chriskp-pdx/COATL-RADAR/Assignments/Exercises/ECE 413 3 Minute Exercises (4_4_2025).docx

Part 1. Constraints and Risks

1. Time. Money, but we don’t need much. Basically have everything we already need.
2. Not much. Testing is slow, but we’re chugging along. We also do have only one prototype currently that is being used for testing, but we are working on making more prototypes.
3. Successfully getting our machine learning program to work. Consistency of amplitude across tests. Testing in general is time-consuming.

Part 2. Mitigations

1. We found our stride already and are on target to complete our “must” requirements.
2. Yes, if we get more prototypes we can work in parallel on testing moving forward.
3. See 2.
