chriskp-pdx/COATL-RADAR/Software/Data Collection/Datasets/Roasted Bean Comparison.docx

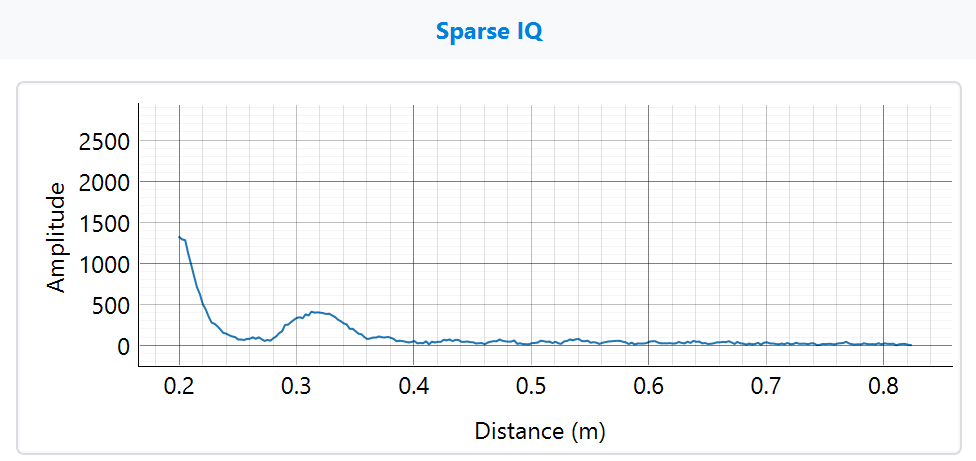
[picture p23: figure]

Dark Roast

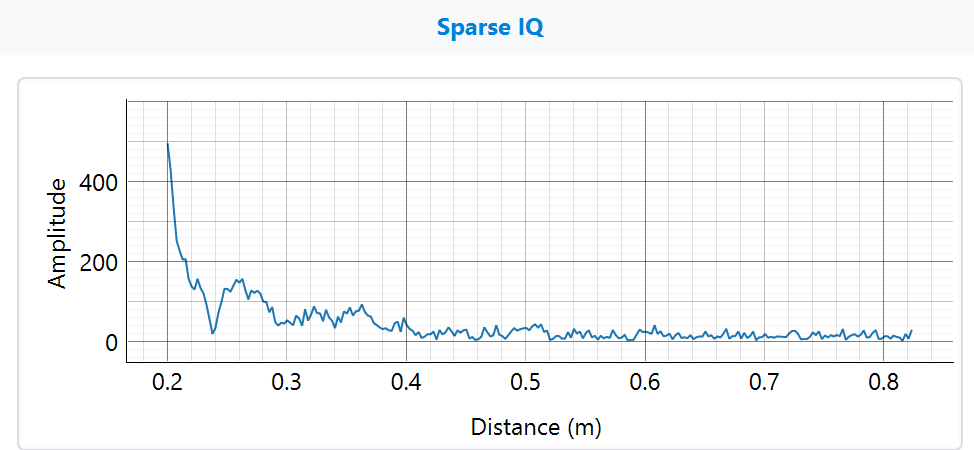
[picture p24: figure]

Medium Roast

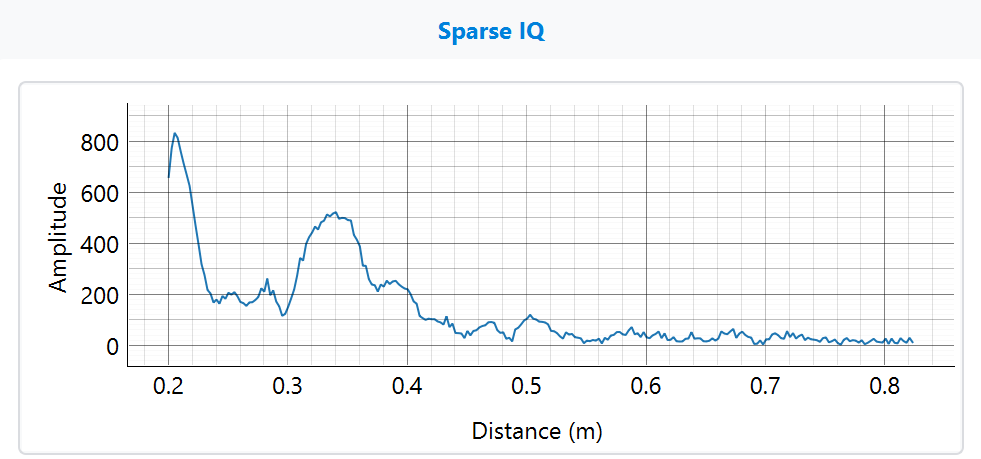
[picture p25: figure]

Light Roast
