chriskp-pdx/COATL-RADAR/Documentation/Test Documentation/Metal Device Testing/1-10 Bean Range Tests/Lens 2 Testing/README.docx

Beanis testing process Lens 2

Each bean type will have the exact same process for each

1. Start with no beans in the Beanis. Take a screenshot.
2. Add one bean. And repeat the process
3. Continue up until desired beans are in the beanis, repeat with other flavors and or lens combinations.
4. Because the beanis was not specifically made for this lens, I will be running through this test twice to simulate different orientations

After each flavor, I stopped and restarted the IQ just to start fresh

The recorded picture for each amount of beans will be found in this drive and sorted by the bean type. This will be a living drive that I will add more bean types to.

The naming convention for photos will be as follows

NameOfCoffee_NumberOfBeans_Before/AfterShaking

Kamal Notes:

Weird change in amplitude around 7 or 8 beans, will need to test this amount more
