chriskp-pdx/COATL-RADAR/Documentation/Test Documentation/Metal Device Testing/1-10 Bean Range Tests/Lens 1 Testing/Bean Testing Part 1.pptx

## Bean Testing

1. Start with no beans in the Beanis. Take a screenshot.
2. To keep consistent, I will be picking up and inverting the Bean-tube to simulate moving the beans around even without any beans in there. Take another screenshot after movement so you have a before shaking and after shaking picture.
3. Add one bean. And repeat the process
4. Continue up until desired beans are in the bean-tube, repeat with other flavors and or lens combinations. (I will be focusing on the lens the bean-tube was modeled for)

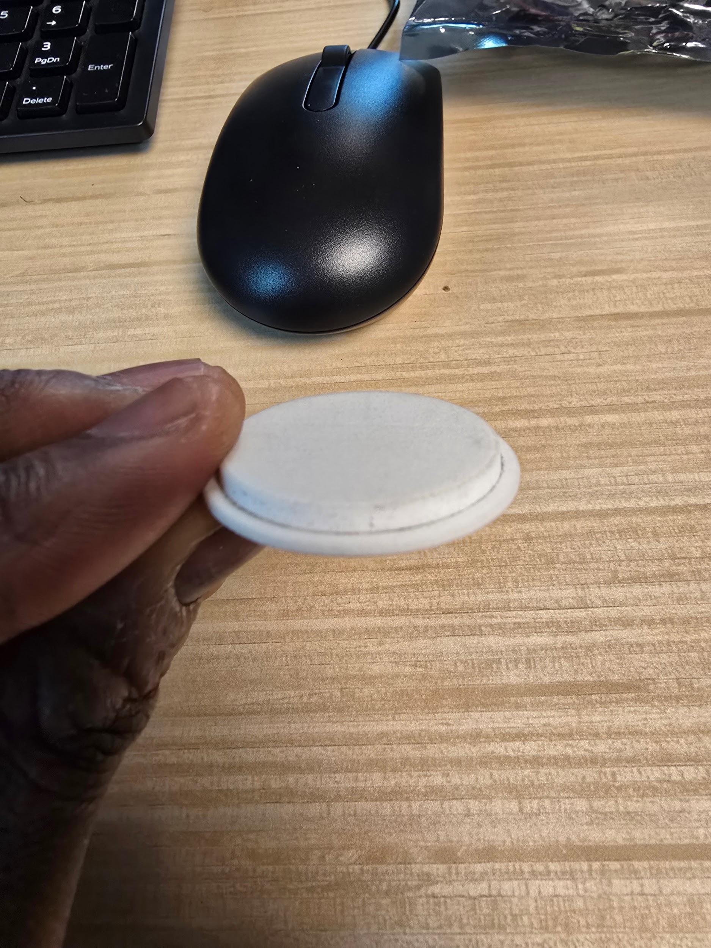
[picture p122: figure]

## Settings

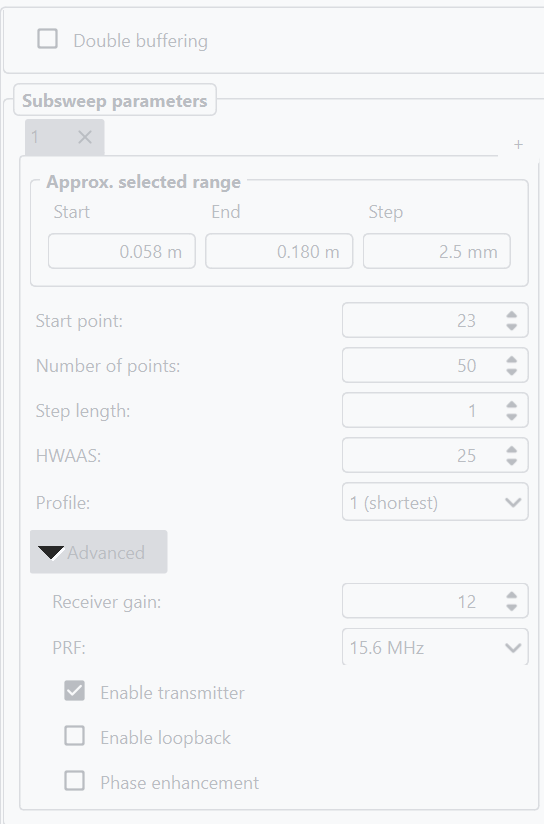
[picture p123: figure]
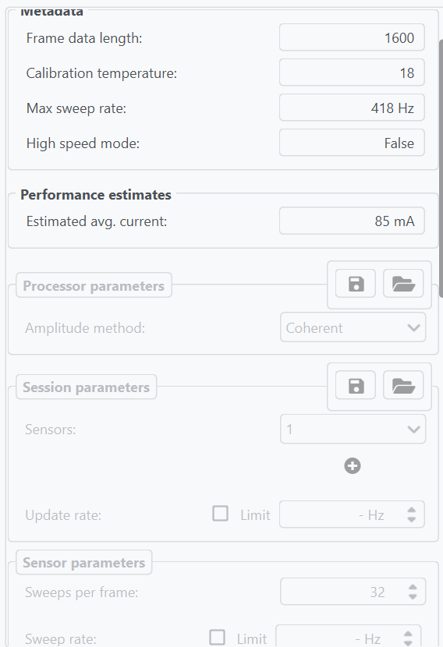
[picture p124: figure]
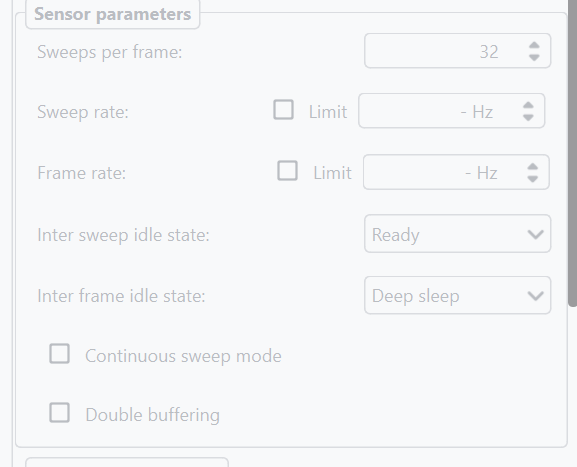
[picture p125: figure]

Notes: Profile
Profiles are used to set the transmitted pulse length in discreet steps. The higher the Profile, the longer the transmitted pulse length.

## Slide 3

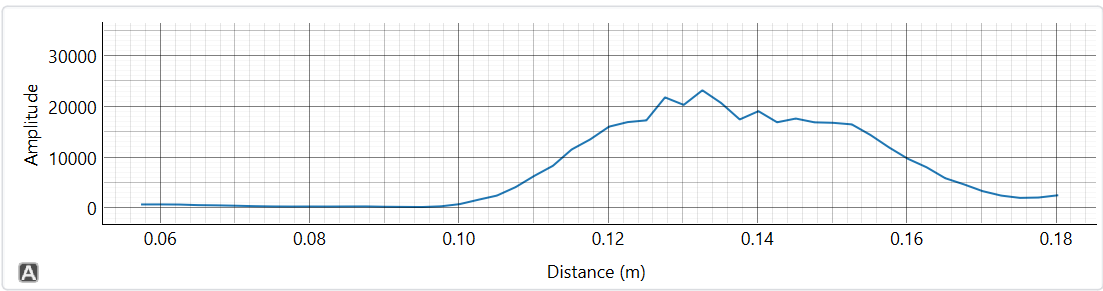
[picture p126: figure]
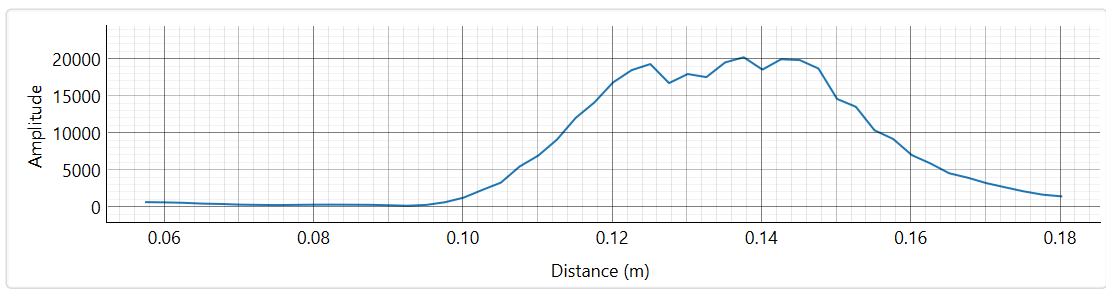
[picture p127: figure]
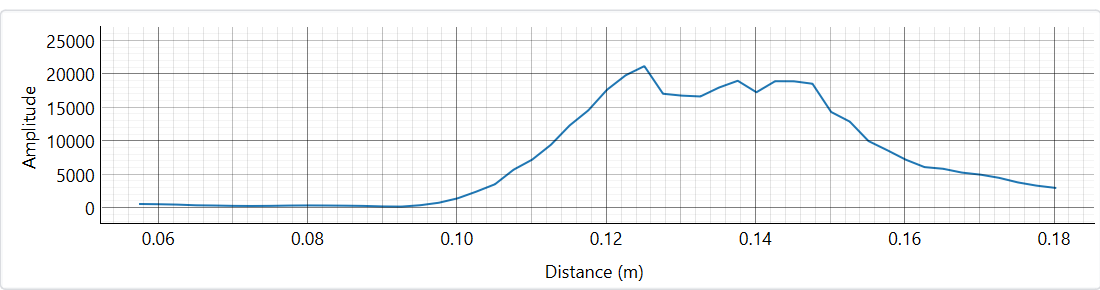
[picture p128: figure]

Notes: Image 1: Tailored no beans roast rite 8.8%
Image 2: Comicovel no beans roastrite 7.6%
Image 3 : Sweet marias no beans Tested on roastrite 9.5%

## One bean

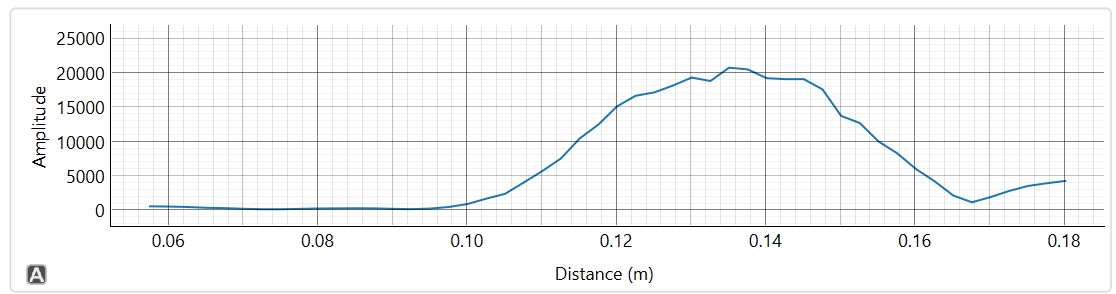
[picture p129: figure]
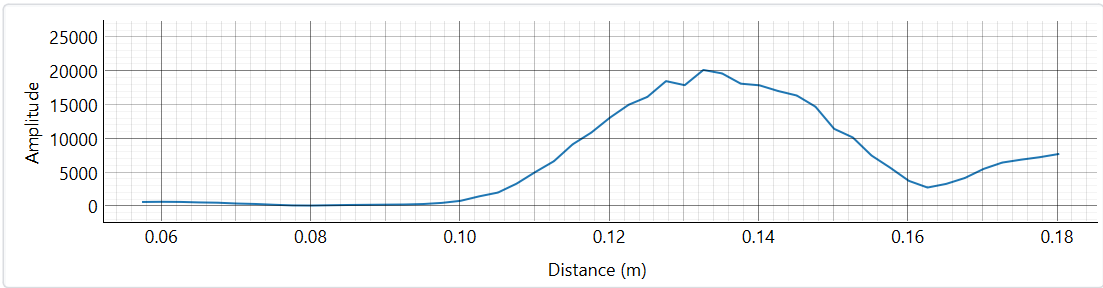
[picture p130: figure]
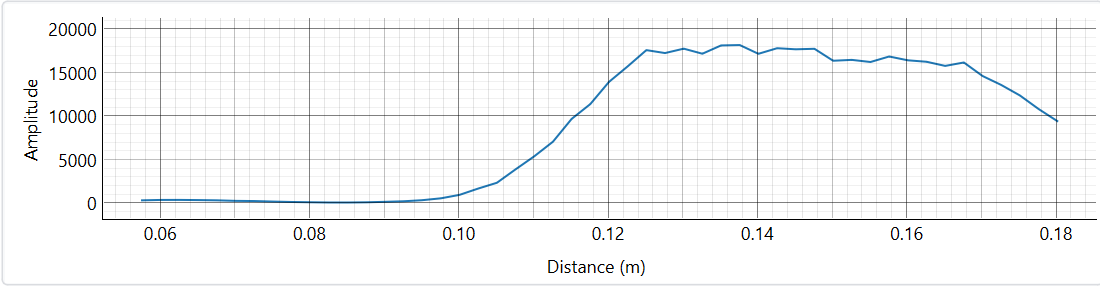
[picture p131: figure]
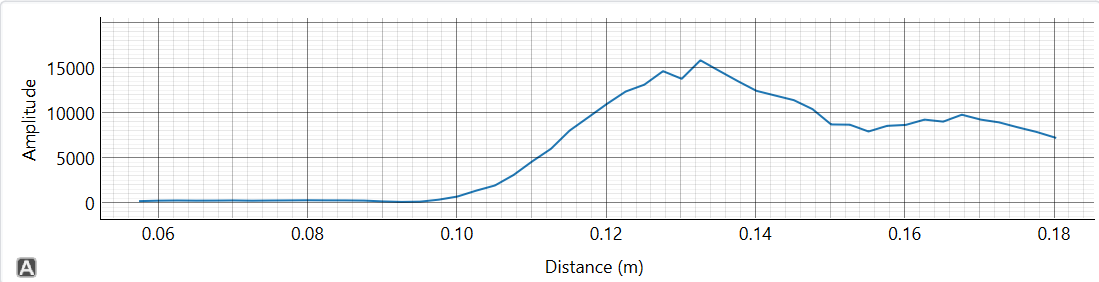
[picture p132: figure]
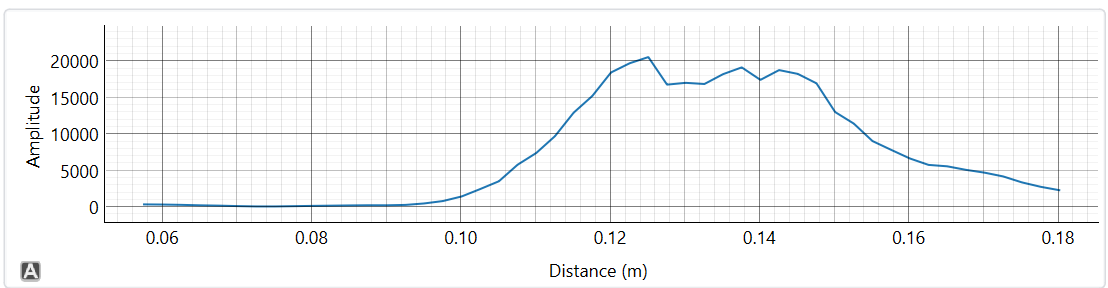
[picture p133: figure]
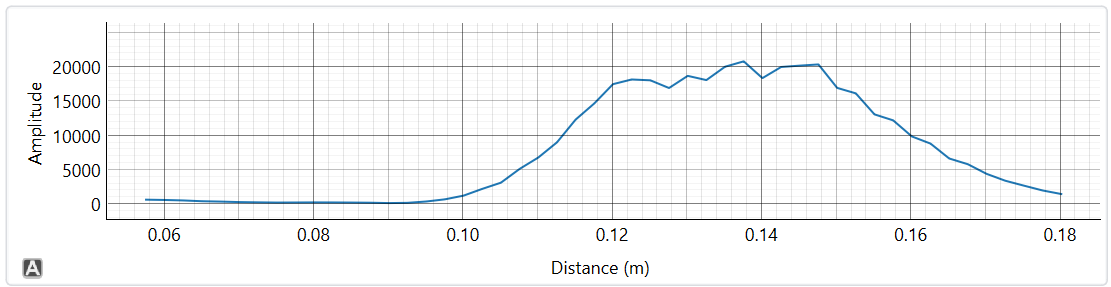
[picture p134: figure]

Notes: Tailored- Image 1 : Before Image 2: After
Comicovel Image 1: Before Image 2: After
Sweet marias Image 1: Before Image 2: After

## Three beans

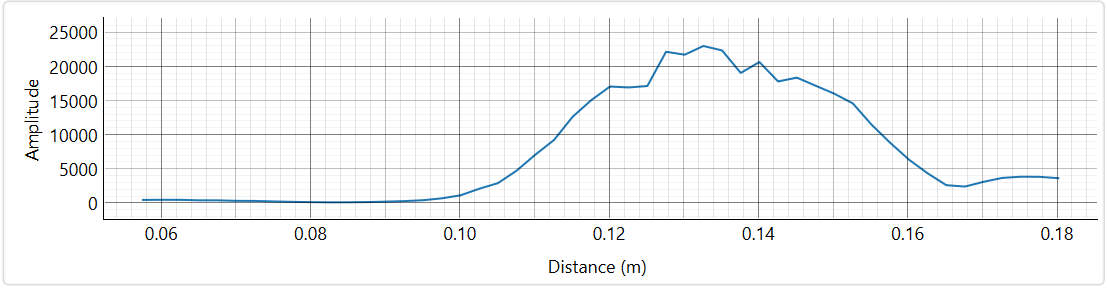
[picture p135: figure]
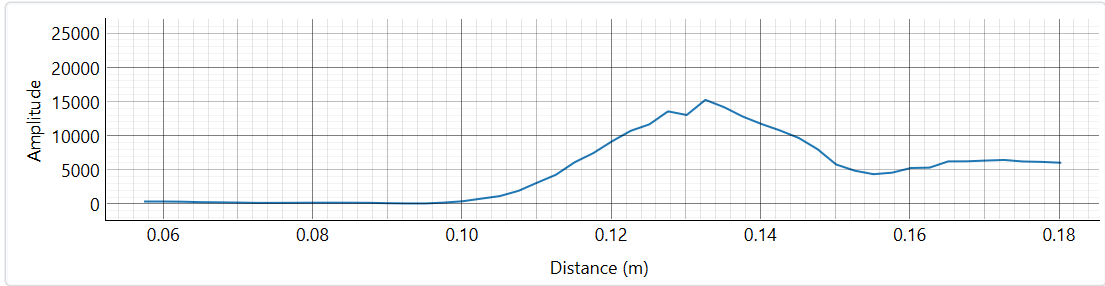
[picture p136: figure]
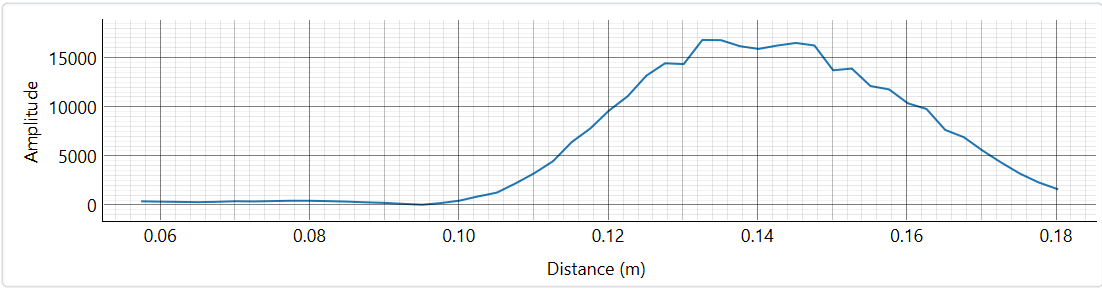
[picture p137: figure]
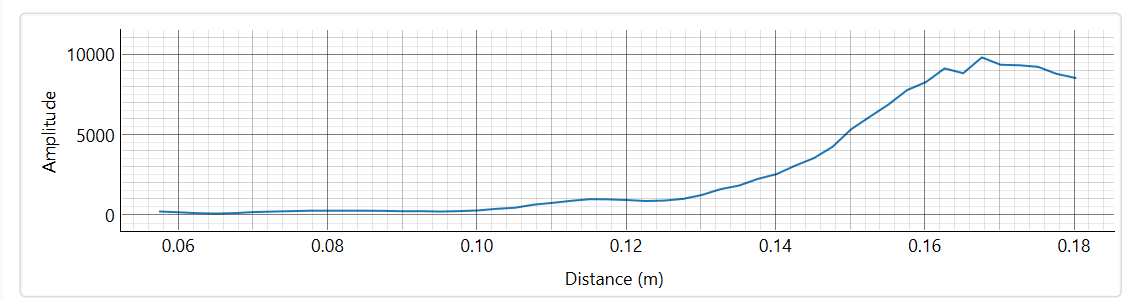
[picture p138: figure]
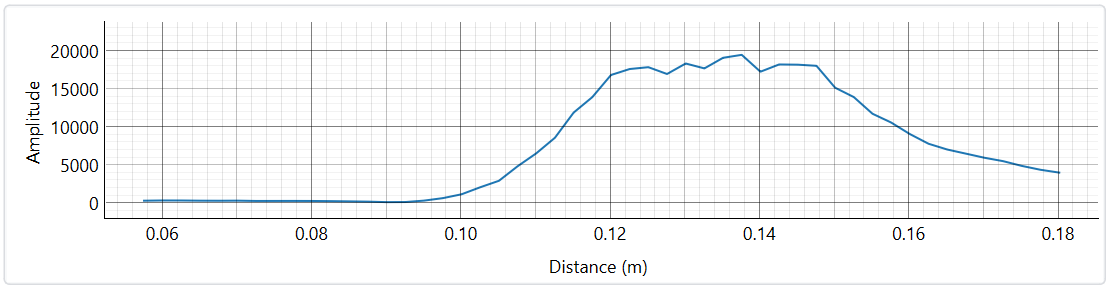
[picture p139: figure]
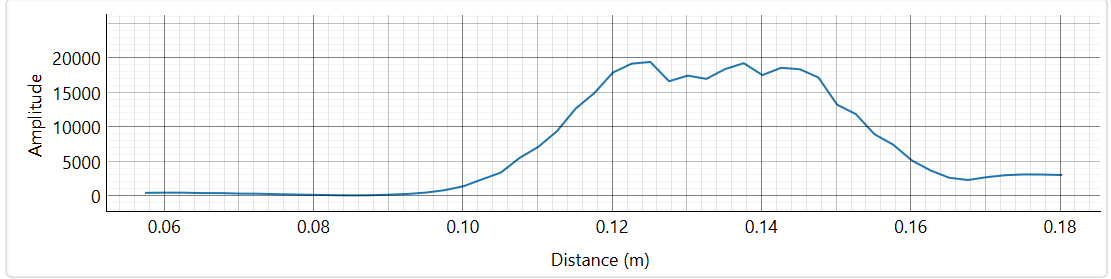
[picture p140: figure]

Notes: Tailored- Image 1 : Before Image 2: After
Comicovel Image 1: Before Image 2: After
Sweet marias Image 1: Before Image 2: After

## Five beans

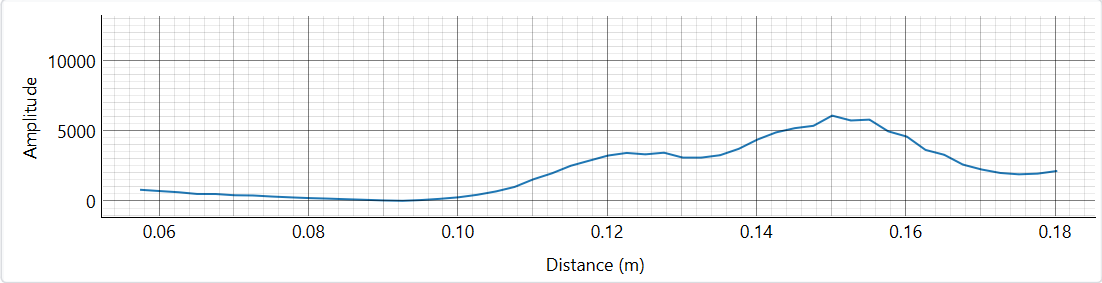
[picture p141: figure]
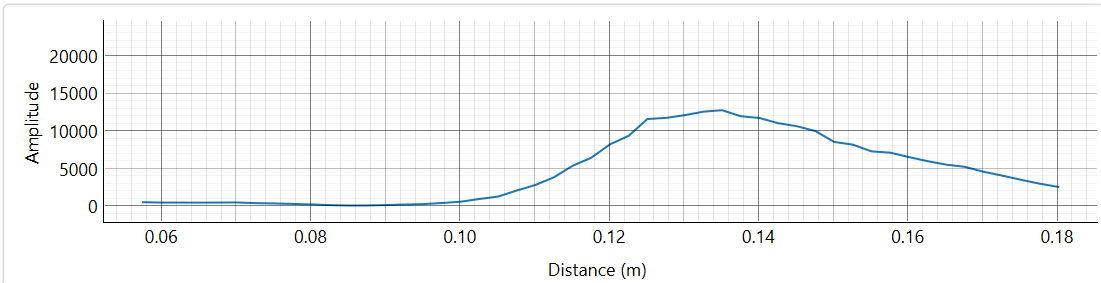
[picture p142: figure]
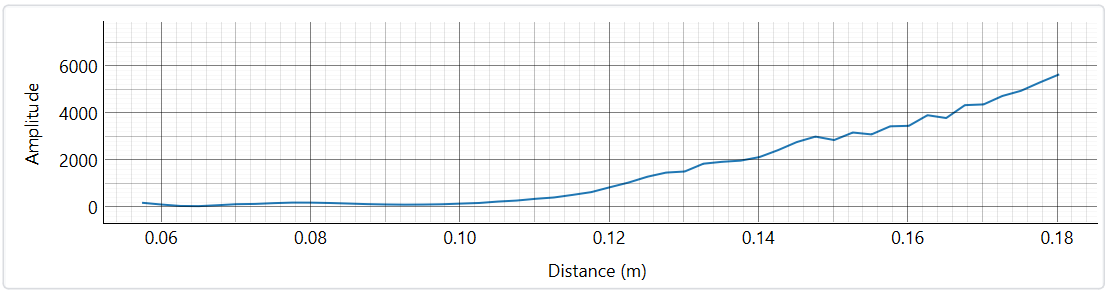
[picture p143: figure]
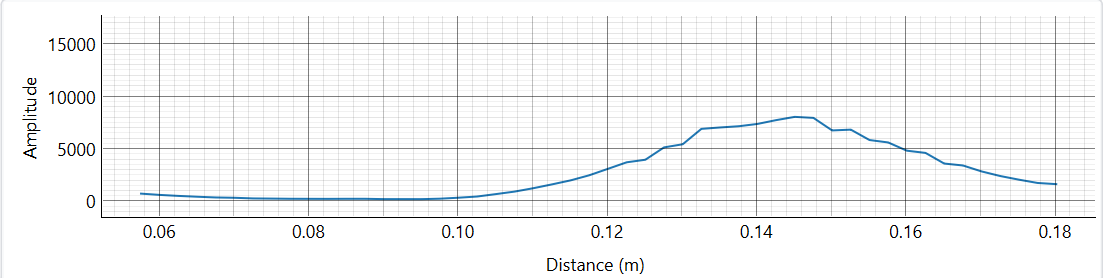
[picture p144: figure]
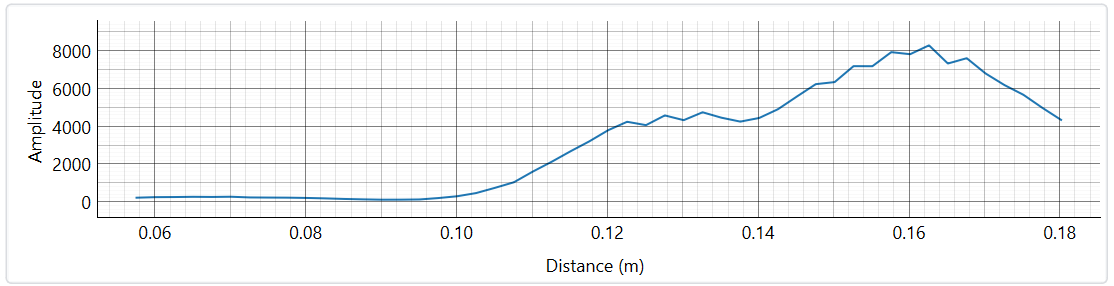
[picture p145: figure]
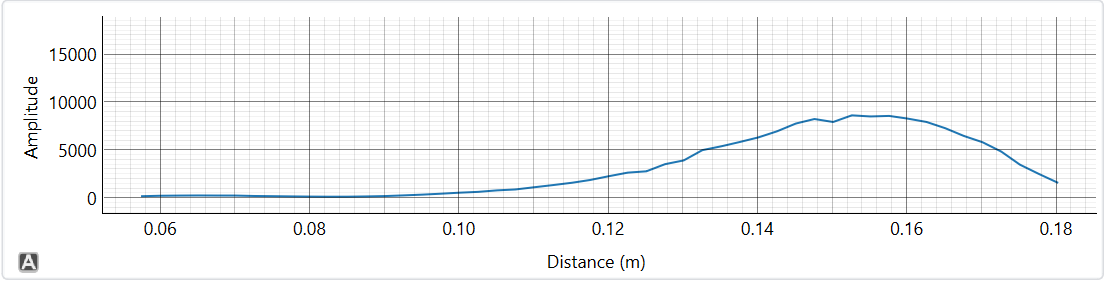
[picture p146: figure]

Notes: Tailored- Image 1 : Before Image 2: After
Comicovel Image 1: Before Image 2: After
Sweet marias Image 1: Before Image 2: After

## Seven Beans

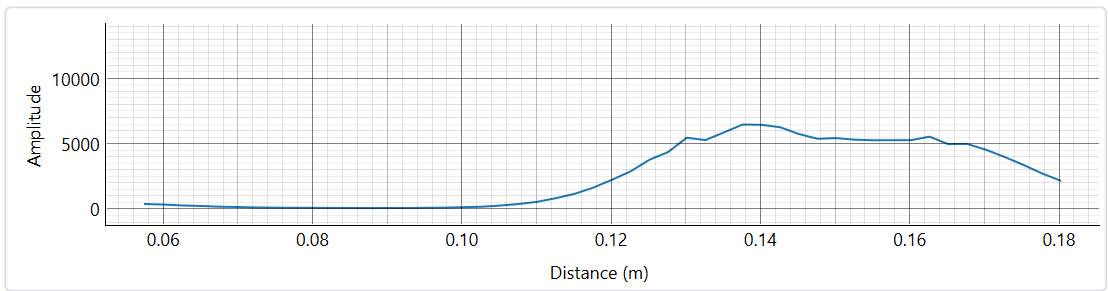
[picture p147: figure]
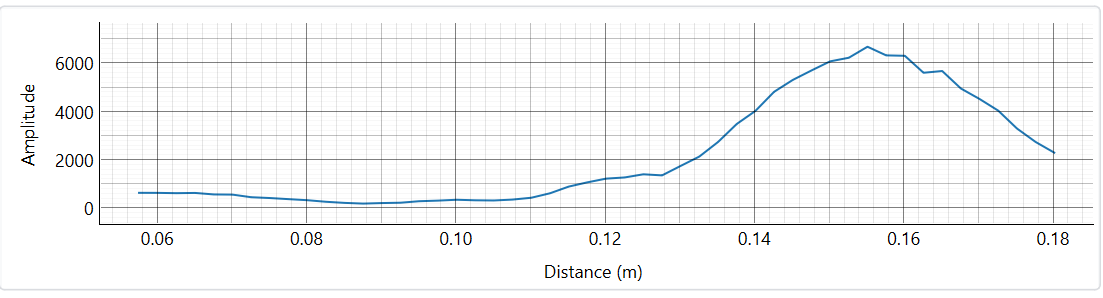
[picture p148: figure]
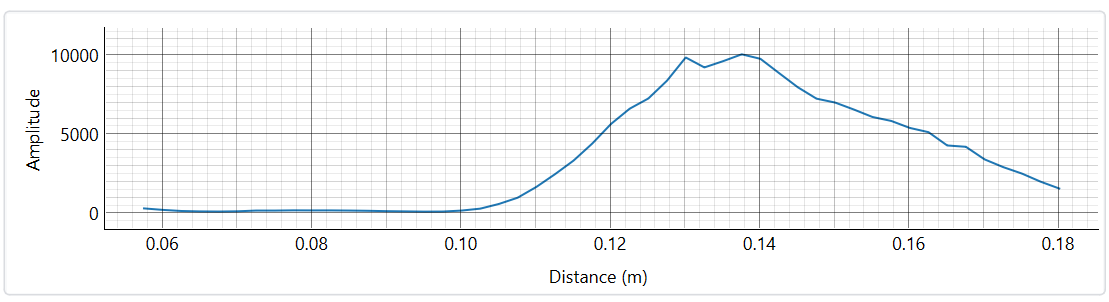
[picture p149: figure]
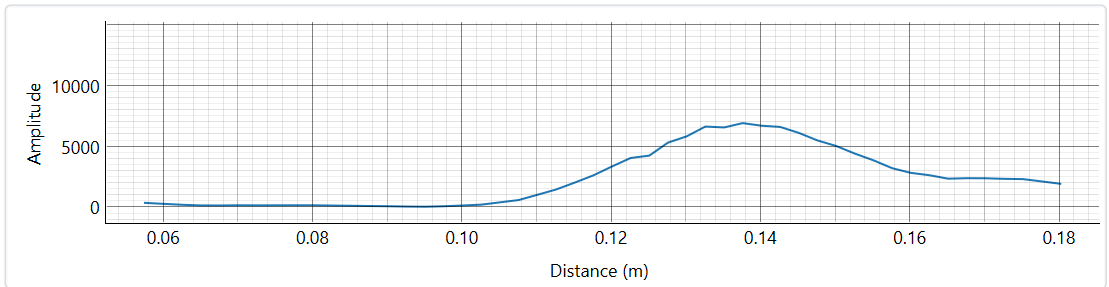
[picture p150: figure]
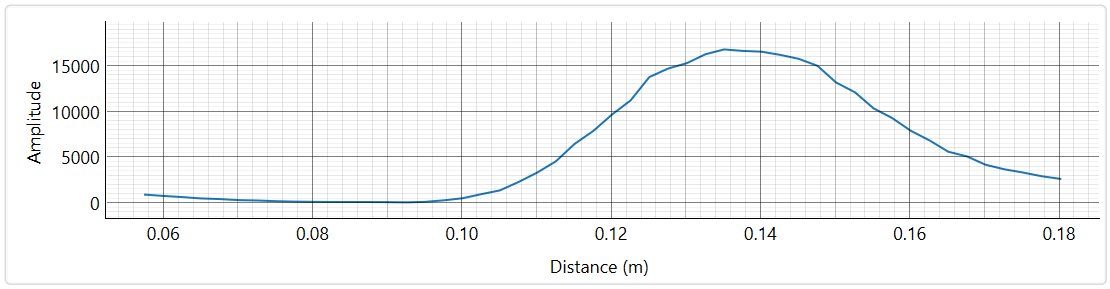
[picture p151: figure]
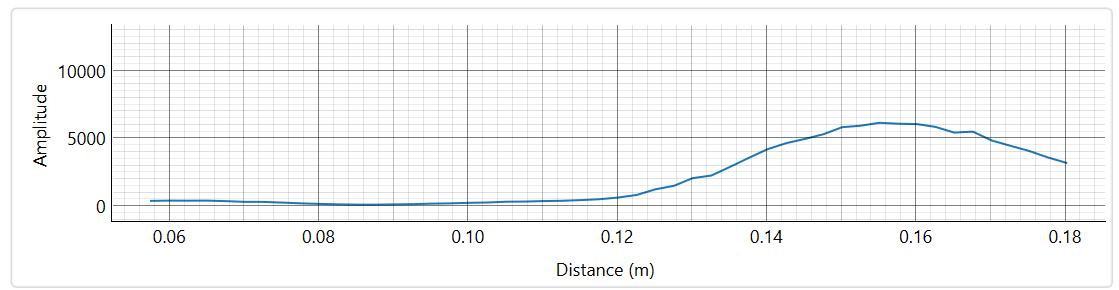
[picture p152: figure]

Notes: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

## Nine Beans

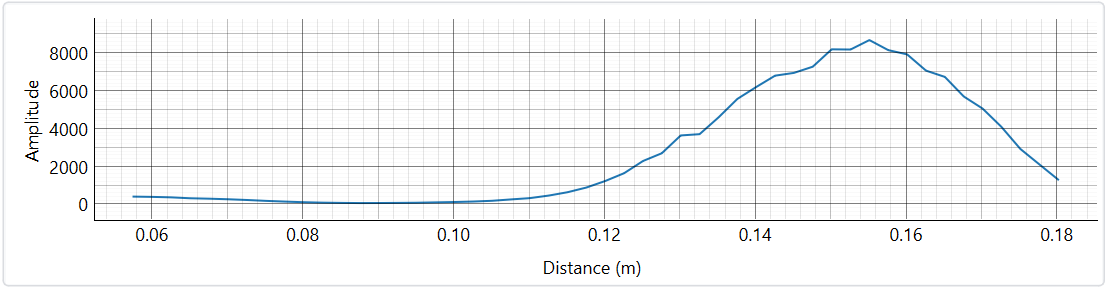
[picture p153: figure]
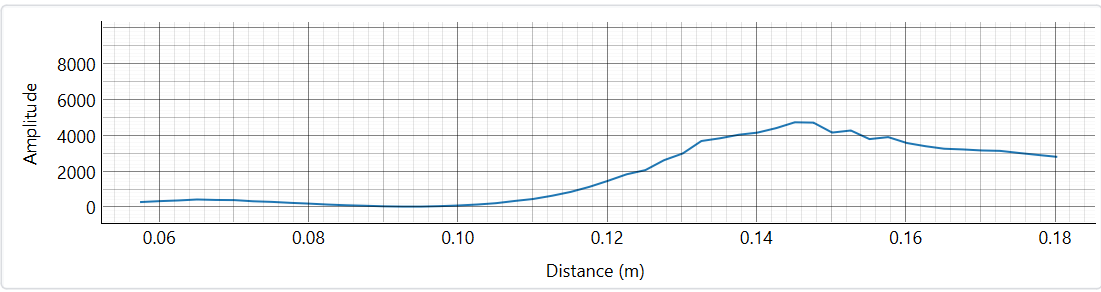
[picture p154: figure]
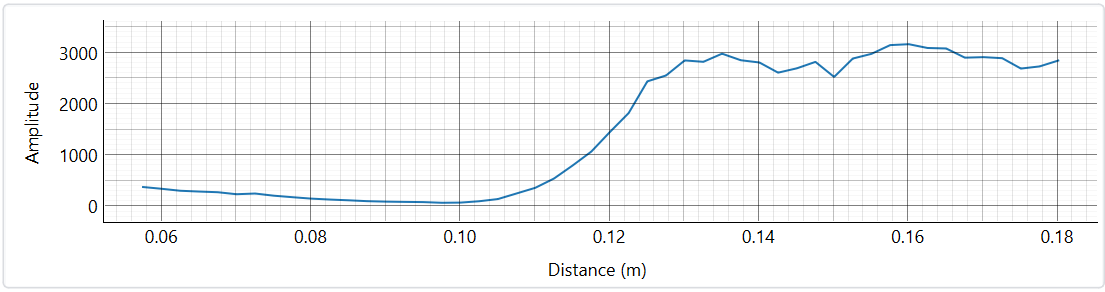
[picture p155: figure]
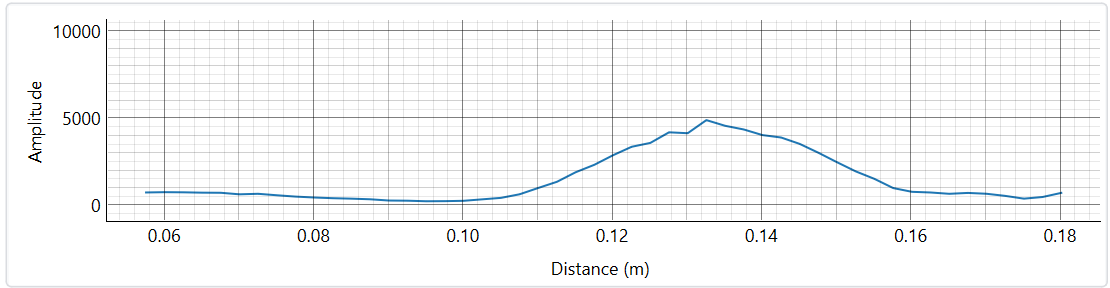
[picture p156: figure]
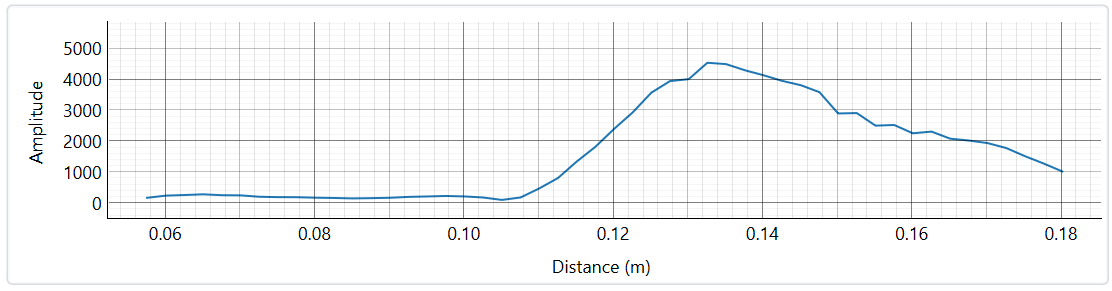
[picture p157: figure]
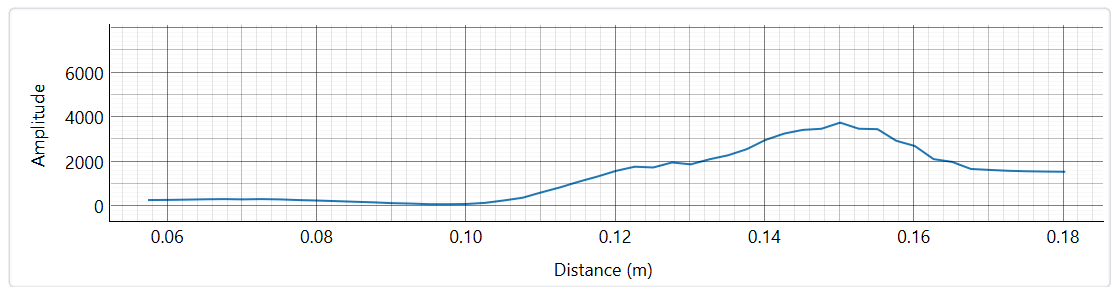
[picture p158: figure]

Notes: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

## Ten Beans

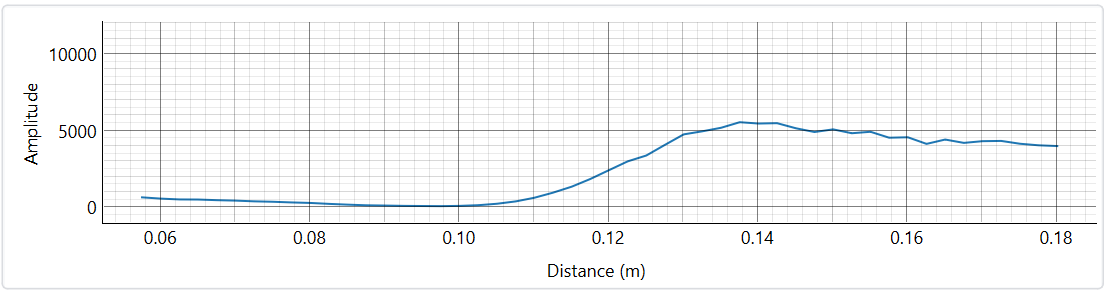
[picture p159: figure]
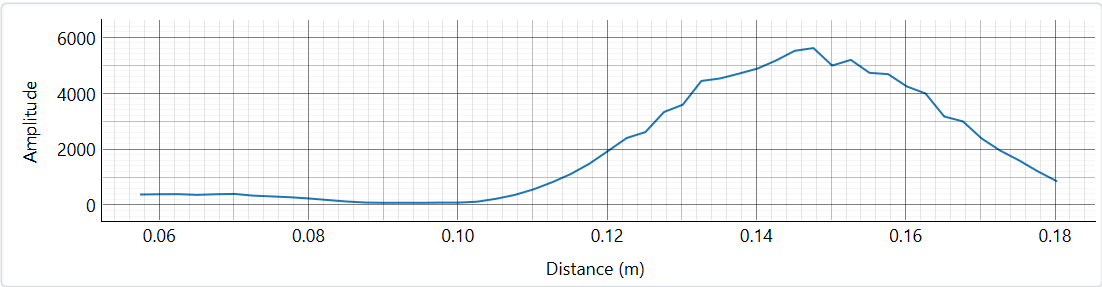
[picture p160: figure]
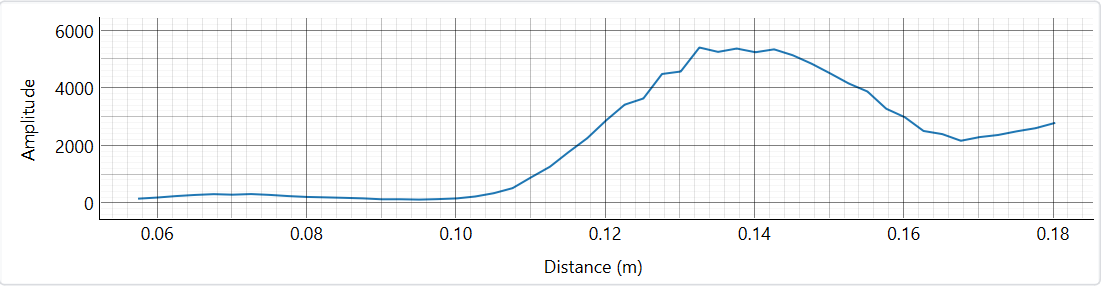
[picture p161: figure]
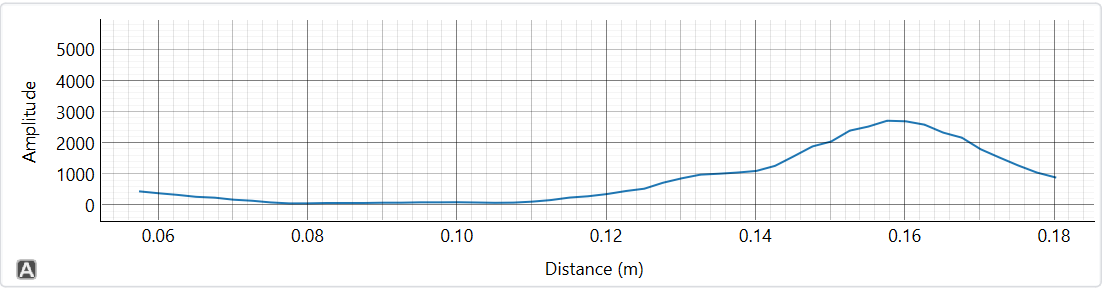
[picture p162: figure]
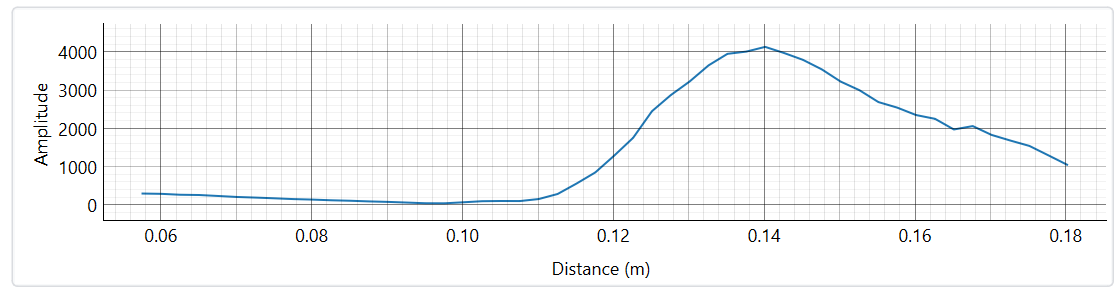
[picture p163: figure]
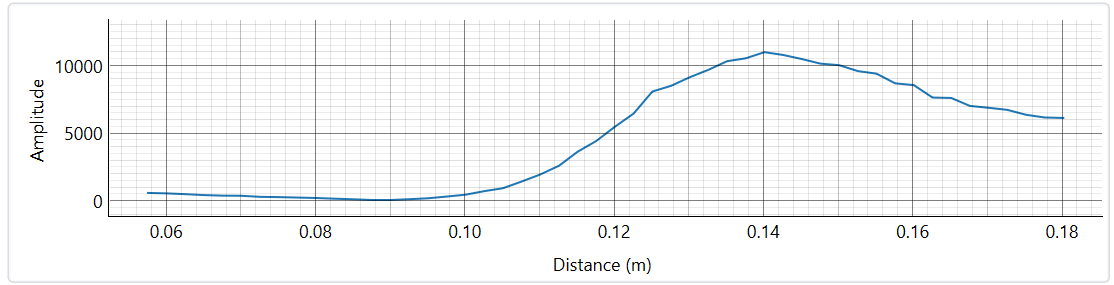
[picture p164: figure]

Notes: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
