chriskp-pdx/COATL-RADAR/Documentation/Test Documentation/Metal Device Testing/Real and Imaginary Testing/Real_and_Imag_testV1.xlsx

Sheet: GuatatemalaAntiguaHunapuCiudadV
RunID | Iteration | RealPart | ImagPart | Magnitude | PhaseRadians
20250417-105007 | 1 | -9848.688 | 5941.182 | 11501.92588 | 2.59878978
20250417-105007 | 2 | -9025.632 | 6833.712 | 11320.85035 | 2.493534416
20250417-105007 | 3 | -9157.05 | 6551.058 | 11259.12633 | 2.520598175
20250417-105007 | 4 | -9714.212 | 5842.88 | 11336.01171 | 2.60008746
20250417-105007 | 5 | -9410.668 | 6142.06 | 11237.6854 | 2.563342796
20250417-105007 | 6 | -9180.852 | 6496.886 | 11247.1139 | 2.525746821
20250417-105007 | 7 | -9283.08 | 6343.822 | 11243.6494 | 2.542111971
20250417-105007 | 8 | -9415.202 | 6092.304 | 11214.37456 | 2.567279254
20250417-105007 | 9 | -8663.43 | 6979.476 | 11125.11144 | 2.463431218
20250417-105007 | 10 | -9275.086 | 6277.94 | 11199.98888 | 2.546565896
20250417-105436 | 1 | 2974.316 | -2410.264 | 3828.306181 | -0.6810256181
20250417-105436 | 2 | 3089.028 | -2196.788 | 3790.510718 | -0.6181755871
20250417-105436 | 3 | 3091.936 | -2180.026 | 3783.197271 | -0.6141194021
20250417-105436 | 4 | 2962.992 | -2420.236 | 3825.815454 | -0.6849142105
20250417-105436 | 5 | 3111.894 | -2211.576 | 3817.715635 | -0.6178610836
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
