chriskp-pdx/COATL-RADAR/Software/Data Collection/Datasets/CombinedBeanDataAll3 - Test.csv

Scan_Group | Point_0 | Point_1 | Point_2 | Point_3 | Point_4 | Point_5 | Point_6 | Point_7 | Point_8 | Point_9 | Point_10 | Point_11 | Point_12 | Point_13 | Point_14 | Point_15 | Point_16 | Point_17 | Point_18 | Point_19 | Point_20 | Point_21 | Point_22 | Point_23 | Point_24 | Point_25 | Point_26 | Point_27 | Point_28 | Point_29 | Point_30 | Point_31 | Point_32 | Point_33 | Point_34 | Point_35 | Point_36 | Point_37 | Point_38 | Point_39 | Point_40 | Point_41 | Point_42 | Point_43 | Point_44 | Point_45 | Point_46 | Point_47 | Point_48 | Point_49 | Point_50 | Point_51 | Point_52 | Point_53 | Point_54 | Point_55 | Point_56 | Point_57 | Point_58
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
