chriskp-pdx/COATL-RADAR/pyFiles/Datasets/MedBeanis_Testing V2 - BEANSV.csv

Scan_Group | Point_0 | Point_1 | Point_2 | Point_3 | Point_4 | Point_5 | Point_6 | Point_7 | Point_8 | Point_9 | Point_10 | Point_11 | Point_12 | Point_13 | Point_14 | Point_15 | Point_16 | Point_17 | Point_18 | Point_19 | Point_20 | Point_21 | Point_22 | Point_23 | Point_24 | Point_25 | Point_26 | Point_27 | Point_28 | Point_29 | Point_30 | Point_31 | Point_32 | Point_33 | Point_34 | Point_35 | Point_36 | Point_37 | Point_38 | Point_39 | Point_40 | Point_41 | Point_42 | Point_43 | Point_44 | Point_45 | Point_46 | Point_47 | Point_48 | Point_49 | Bean Name
Real_1 | 29478.72 | 32443.86 | 29197.16 | 30249.8 | 30455.56 | 29505.9 | 32060.42 | 32882.96 | 31621.26 | 32426.14 | 32613.9 | 30831.54 | 31905.02 | 32061.66 | 32876.46 | 32182.2 | 31473.78 | 32206.2 | 33064.64 | 32289.96 | 32823.3 | 33190.1 | 33845.08 | 34884.46 | 34634.84 | 35986.24 | 35710.02 | 35191.7 | 23929.24 | 27466.7 | -27323.36 | -29497.62 | -22293.6 | -28434.18 | -28816.1 | 7829.92 | -18959.28 | -17747.3 | -28314.24 | -14097.96 | 11683.62 | 4480.24 | -9803.98 | 26973.82 | 24771.84 | 24572.88 | 17881.44 | -11567.84 | 6726.56 | -32895.94 | Rwanda
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
