chriskp-pdx/COATL-RADAR/Documentation/Test Documentation/Metal Device Testing/Large Amount Bean Testing (V1)/README.docx

Currently testing around 40-50 beans in beantube. Modified the settings to actually see this amount

Rather than shaking the Beantube, I am just rotating it directly on the lens as this is giving massively different results

I am going to place some marks on the beantube so I can accurately rotate the device to the same location each time. I will be rotating the device 3 times per bean type

Screenshotting every quarter turn that I do so each bean type will have 4 pictures each. I will go through each bean type a few times and then compare them.
