chriskp-pdx/COATL-RADAR/Documentation/Test Documentation/3D Printed Prototype Testing/1-10 Bean Range Tests/Lens 1 Testing/Comicovel/Profile 1 Tests/Comicovel_Eight_After.png

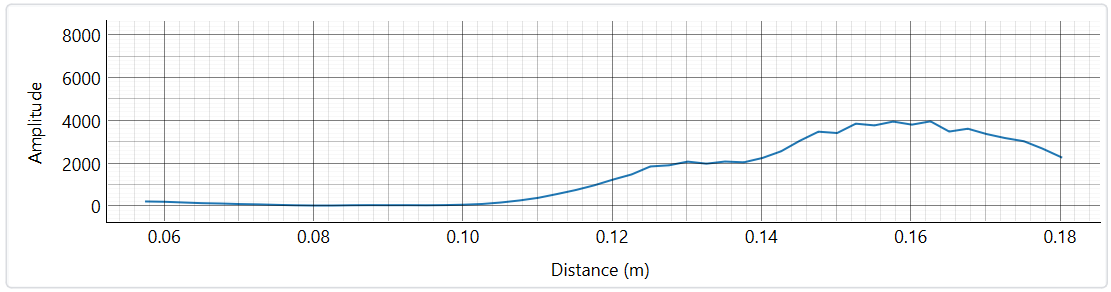
Documentation/Test Documentation/3D Printed Prototype Testing/1-10 Bean Range Tests/Lens 1 Testing/Comicovel/Profile 1 Tests/Comicovel_Eight_After.png
