chriskp-pdx/COATL-RADAR/Documentation/Test Documentation/3D Printed Prototype Testing/1-10 Bean Range Tests/Lens 1 Testing/No beans/Profile 2 Tests/Tailored_NoBeans_After.png

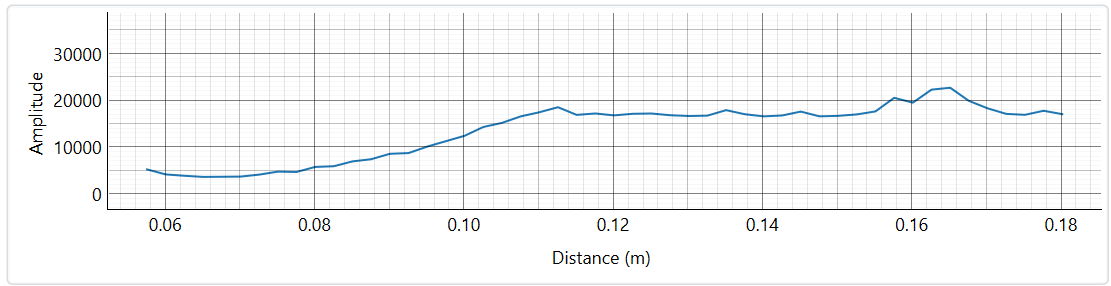
Documentation/Test Documentation/3D Printed Prototype Testing/1-10 Bean Range Tests/Lens 1 Testing/No beans/Profile 2 Tests/Tailored_NoBeans_After.png
