chriskp-pdx/COATL-RADAR/Documentation/Test Documentation/3D Printed Prototype Testing/1-10 Bean Range Tests/Lens 1 Testing/SweetMarias/Profile 1 Tests/SweetMarias_Six_Before.png

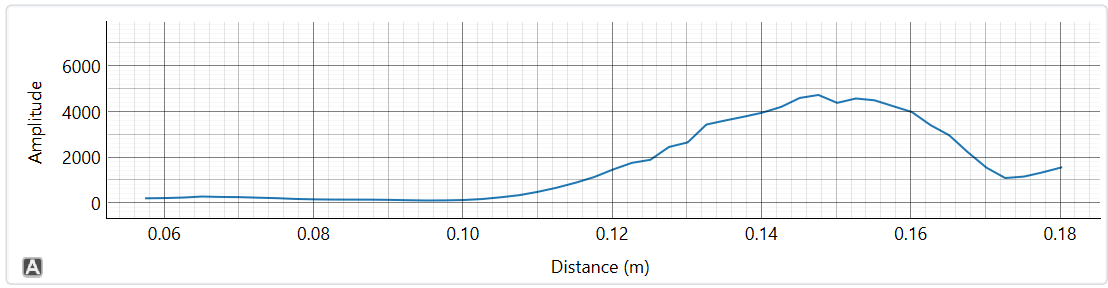
Documentation/Test Documentation/3D Printed Prototype Testing/1-10 Bean Range Tests/Lens 1 Testing/SweetMarias/Profile 1 Tests/SweetMarias_Six_Before.png
