chriskp-pdx/COATL-RADAR/Documentation/Test Documentation/3D Printed Prototype Testing/1-10 Bean Range Tests/Lens 1 Testing/TailoredPulped/Profile 2 Tests/Tailored_Eight_After.png

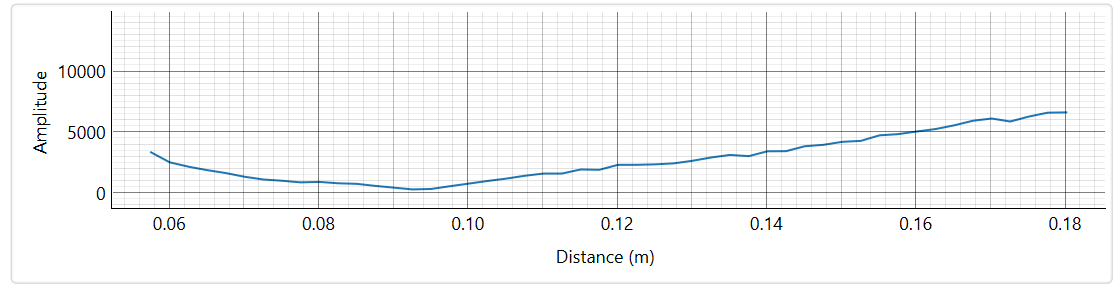
Documentation/Test Documentation/3D Printed Prototype Testing/1-10 Bean Range Tests/Lens 1 Testing/TailoredPulped/Profile 2 Tests/Tailored_Eight_After.png
