chriskp-pdx/COATL-RADAR/Documentation/Test Documentation/3D Printed Prototype Testing/1-10 Bean Range Tests/Lens 1 Testing/Used Settings/Profile 2/Screenshot 2025-03-10 125634.png

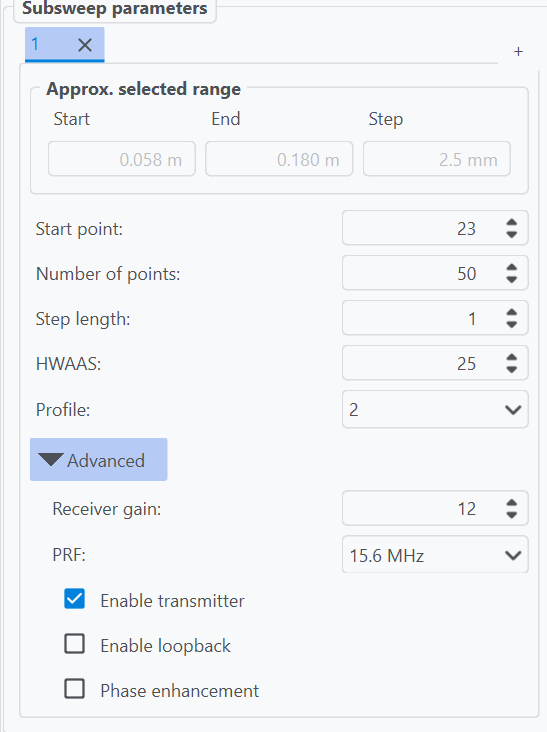
Documentation/Test Documentation/3D Printed Prototype Testing/1-10 Bean Range Tests/Lens 1 Testing/Used Settings/Profile 2/Screenshot 2025-03-10 125634.png
