chriskp-pdx/COATL-RADAR/Documentation/Test Documentation/3D Printed Prototype Testing/1-10 Bean Range Tests/Lens 2 Testing/Comicovel/Profile 1/Comicovel_Five_After.png

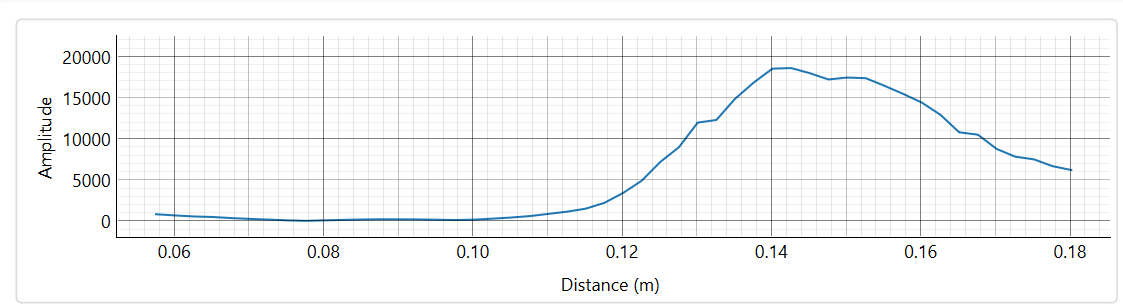
Documentation/Test Documentation/3D Printed Prototype Testing/1-10 Bean Range Tests/Lens 2 Testing/Comicovel/Profile 1/Comicovel_Five_After.png
