chriskp-pdx/COATL-RADAR/Documentation/Test Documentation/3D Printed Prototype Testing/1-10 Bean Range Tests/Lens 2 Testing/Settings Used/Profile 2/Copy of Screenshot 2025-03-10 125538.png

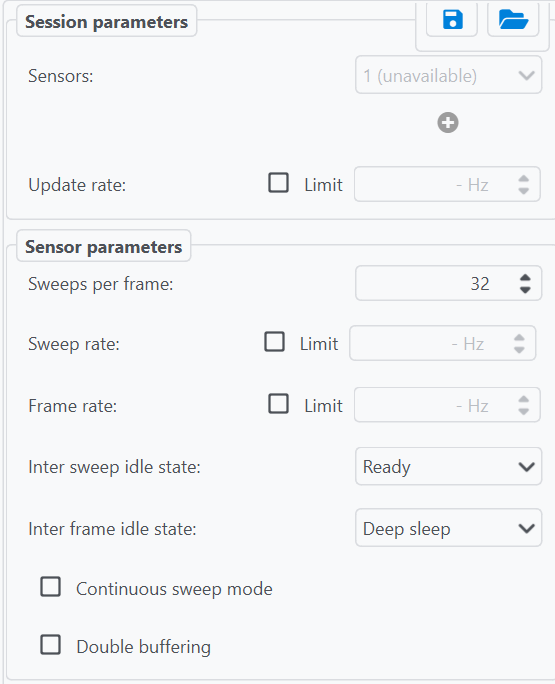
Documentation/Test Documentation/3D Printed Prototype Testing/1-10 Bean Range Tests/Lens 2 Testing/Settings Used/Profile 2/Copy of Screenshot 2025-03-10 125538.png
