chriskp-pdx/COATL-RADAR/Documentation/Test Documentation/Metal Device Testing/1-10 Bean Range Tests/Lens 1 Testing/Comicovel/Profile 1 Tests/Comicovel_Six_Before.png

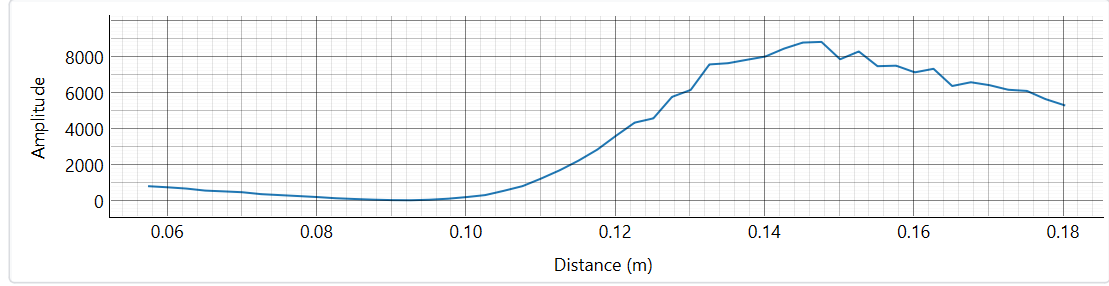
Documentation/Test Documentation/Metal Device Testing/1-10 Bean Range Tests/Lens 1 Testing/Comicovel/Profile 1 Tests/Comicovel_Six_Before.png
