chriskp-pdx/COATL-RADAR/Documentation/Test Documentation/Metal Device Testing/1-10 Bean Range Tests/Lens 1 Testing/Comicovel/Profile 2 Tests/Comicovel_Eight_Before.png

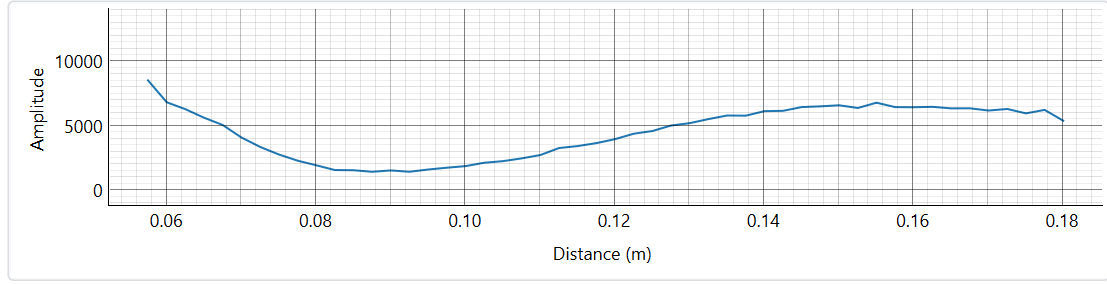
Documentation/Test Documentation/Metal Device Testing/1-10 Bean Range Tests/Lens 1 Testing/Comicovel/Profile 2 Tests/Comicovel_Eight_Before.png
