chriskp-pdx/COATL-RADAR/Documentation/Test Documentation/Metal Device Testing/1-10 Bean Range Tests/Lens 1 Testing/No beans/Profile 2 Tests/Comicovel_NoBeans_Before.png

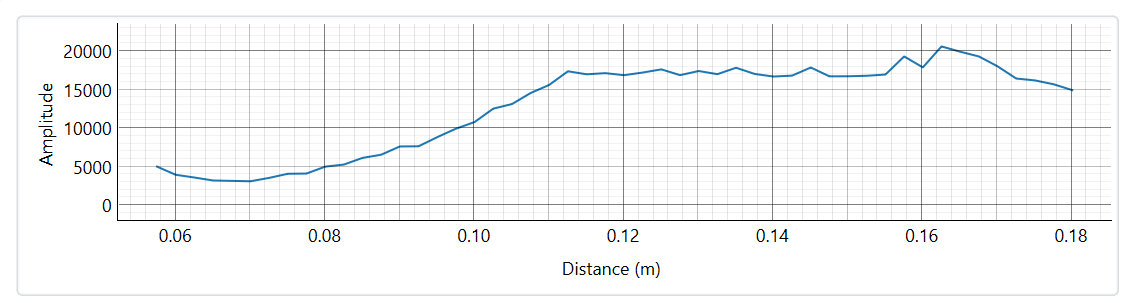
Documentation/Test Documentation/Metal Device Testing/1-10 Bean Range Tests/Lens 1 Testing/No beans/Profile 2 Tests/Comicovel_NoBeans_Before.png
