chriskp-pdx/COATL-RADAR/Documentation/Test Documentation/Metal Device Testing/1-10 Bean Range Tests/Lens 1 Testing/SweetMarias/Profile 2 Tests/Screenshot 2025-03-10 132043.png

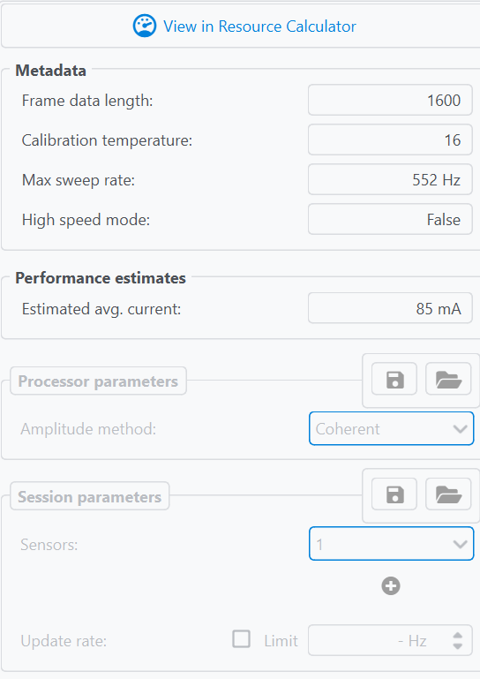
Documentation/Test Documentation/Metal Device Testing/1-10 Bean Range Tests/Lens 1 Testing/SweetMarias/Profile 2 Tests/Screenshot 2025-03-10 132043.png
