chriskp-pdx/COATL-RADAR/Documentation/Test Documentation/Metal Device Testing/1-10 Bean Range Tests/Lens 1 Testing/TailoredPulped/Profile 1 Tests/Tailored_Two_Before.png

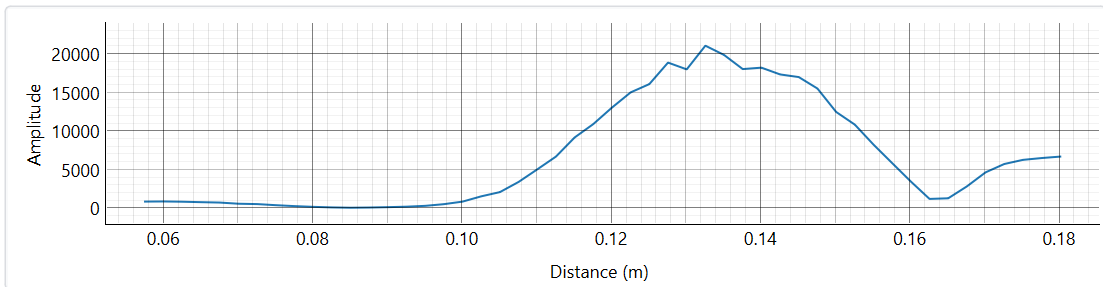
Documentation/Test Documentation/Metal Device Testing/1-10 Bean Range Tests/Lens 1 Testing/TailoredPulped/Profile 1 Tests/Tailored_Two_Before.png
