chriskp-pdx/COATL-RADAR/Documentation/Test Documentation/Thin Metal Device Testing/1-10 Bean Range Tests/Profile 1/Flat Lens Testing/Zero Bean Baseline/FlatLens_ZeroBean_After.png

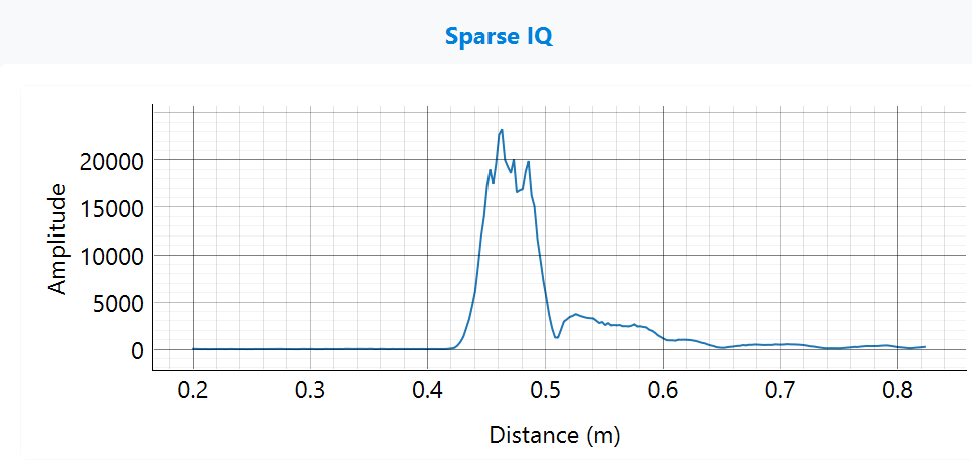
Documentation/Test Documentation/Thin Metal Device Testing/1-10 Bean Range Tests/Profile 1/Flat Lens Testing/Zero Bean Baseline/FlatLens_ZeroBean_After.png
