chriskp-pdx/COATL-RADAR/Documentation/Test Documentation/Thin Metal Device Testing/1-10 Bean Range Tests/Profile 1/FZP Lens Testing/Comicovel/Comicovel_Three_Before.png

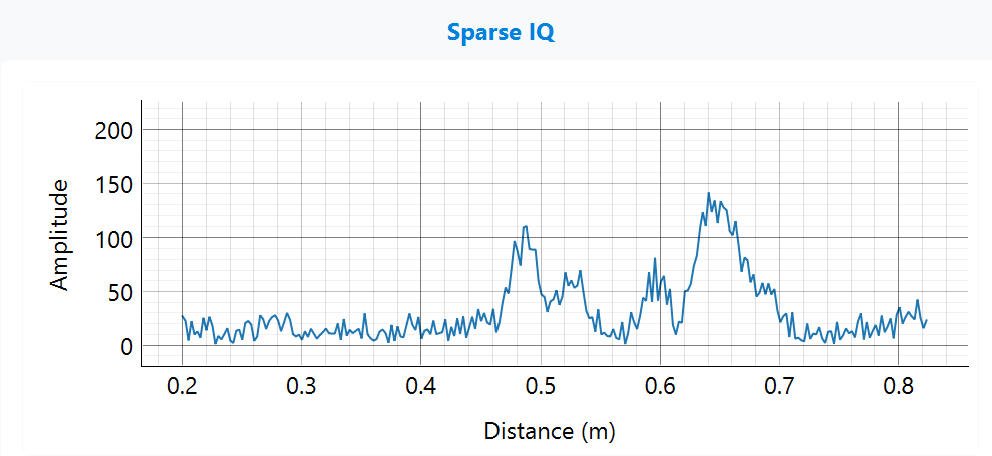
Documentation/Test Documentation/Thin Metal Device Testing/1-10 Bean Range Tests/Profile 1/FZP Lens Testing/Comicovel/Comicovel_Three_Before.png
