chriskp-pdx/COATL-RADAR/Documentation/Test Documentation/Thin Metal Device Testing/1-10 Bean Range Tests/Profile 1/FZP Lens Testing/Ethiopiques/Ethiopiques_Five_Before.png

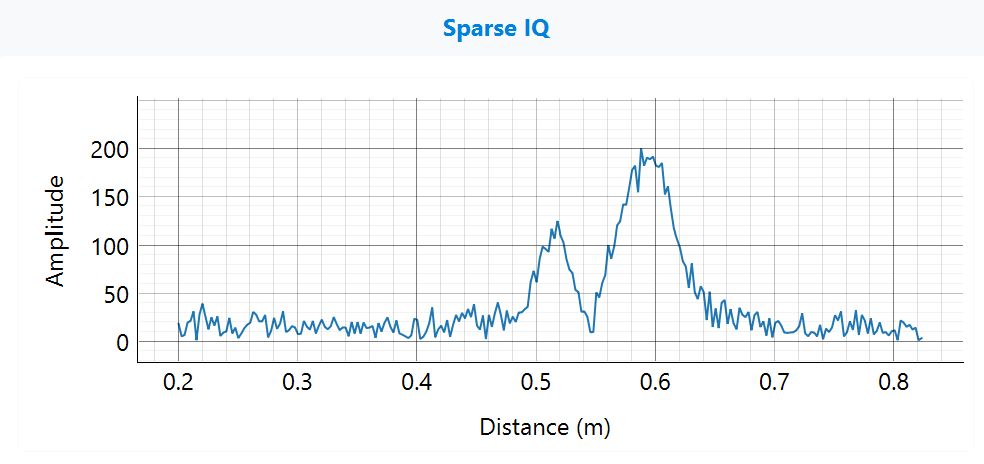
Documentation/Test Documentation/Thin Metal Device Testing/1-10 Bean Range Tests/Profile 1/FZP Lens Testing/Ethiopiques/Ethiopiques_Five_Before.png
