chriskp-pdx/COATL-RADAR/Documentation/Test Documentation/Thin Metal Device Testing/1-10 Bean Range Tests/Profile 1/Hyperbolic Lens Testing/Comicovel/Comicovel_Nine_Before.png

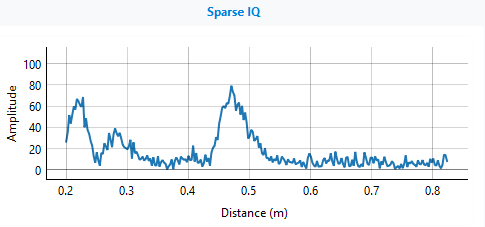
Documentation/Test Documentation/Thin Metal Device Testing/1-10 Bean Range Tests/Profile 1/Hyperbolic Lens Testing/Comicovel/Comicovel_Nine_Before.png
