chriskp-pdx/COATL-RADAR/Documentation/Test Documentation/Thin Metal Device Testing/Large Amount of Bean Tests/Profile 2/Flat Lens Testing/Zero Bean Baseline/FlatLens_ZeroBean_After.png

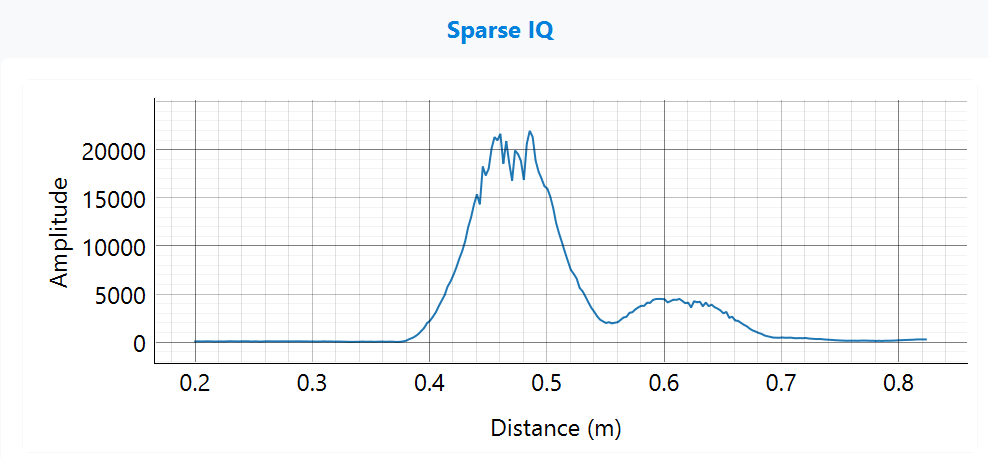
Documentation/Test Documentation/Thin Metal Device Testing/Large Amount of Bean Tests/Profile 2/Flat Lens Testing/Zero Bean Baseline/FlatLens_ZeroBean_After.png
